Johannf78/Open-Energy-Gateway/src/open_energy_gateway/web_home.h

//Raw string literal quotation, webpage HTML...

String webpage_home = R"(

<!-- Main Content -->
<main class="main-content">
  
  <!-- Header -->
  <header class="header">
    <h1>Home</h1>
  </header>

  <!-- Content -->
  <div class="content">

  <div class="card">
    <p>Connection status: <span id="connection_status" style="color: gray;">Connecting...</span></p>
    <p>Last update: <span id="last_update">--:--:--</span></p>
    <br>
    <p>Values updates every 5 seconds. Initial connection usually takes a few seconds.</p>  
  </div>


  <div class="card">
  <h2>Meter List</h2>
  <p>(Connection typically completes in 2-8 seconds)</p>
    <table>
      <thead>
        <tr>
          <th>Meter</th>
          <th>Serial Number</th>
          <th>Name</th>
          <th>View</th>
        </tr>
      </thead>
      <tbody>
        <tr id="meter-list-row-1">
          <td>1</td>
          <td id="meter_list_m1_serial_number">Loading...</td>
          <td id="meter_list_m1_name" style="text-align: left;">Loading...</td>
          <td><a href="/meters?id=1" class="view-button">View</a></td>
        </tr>
        <tr id="meter-list-row-2">
          <td>2</td>
          <td id="meter_list_m2_serial_number">Loading...</td>
          <td id="meter_list_m2_name" style="text-align: left;">Loading...</td>
          <td><a href="/meters?id=2" class="view-button">View</a></td>
        </tr>
        <tr id="meter-list-row-3">
          <td>3</td>
          <td id="meter_list_m3_serial_number">Loading...</td>
          <td id="meter_list_m3_name" style="text-align: left;">Loading...</td>
          <td><a href="/meters?id=3" class="view-button">View</a></td>
        </tr>
        <tr id="meter-list-row-4">
          <td>4</td>
          <td id="meter_list_m4_serial_number">Loading...</td>
          <td id="meter_list_m4_name" style="text-align: left;">Loading...</td>
          <td><a href="/meters?id=4" class="view-button">View</a></td>
        </tr>
        <tr id="meter-list-row-5">
          <td>5</td>
          <td id="meter_list_m5_serial_number">Loading...</td>
          <td id="meter_list_m5_name" style="text-align: left;">Loading...</td>
          <td><a href="/meters?id=5" class="view-button">View</a></td>
        </tr>
        <tr id="meter-list-row-6">
          <td>6</td>
          <td id="meter_list_m6_serial_number">Loading...</td>
          <td id="meter_list_m6_name" style="text-align: left;">Loading...</td>
          <td><a href="/meters?id=6" class="view-button">View</a></td>
        </tr>
        <tr id="meter-list-row-7">
          <td>7</td>
          <td id="meter_list_m7_serial_number">Loading...</td>
          <td id="meter_list_m7_name" style="text-align: left;">Loading...</td>
          <td><a href="/meters?id=7" class="view-button">View</a></td>
        </tr>
        <tr id="meter-list-row-8">
          <td>8</td>
          <td id="meter_list_m8_serial_number">Loading...</td>
          <td id="meter_list_m8_name" style="text-align: left;">Loading...</td>
          <td><a href="/meters?id=8" class="view-button">View</a></td>
        </tr>
        <tr id="meter-list-row-9">
          <td>9</td>
          <td id="meter_list_m9_serial_number">Loading...</td>
          <td id="meter_list_m9_name" style="text-align: left;">Loading...</td>
          <td><a href="/meters?id=9" class="view-button">View</a></td>
        </tr>
        <tr id="meter-list-row-10">
          <td>10</td>
          <td id="meter_list_m10_serial_number">Loading...</td>
          <td id="meter_list_m10_name" style="text-align: left;">Loading...</td>
          <td><a href="/meters?id=10" class="view-button">View</a></td>
        </tr>
      </tbody>
    </table>
  </div>
  
<div class="card">
  <h2>Energy Consumption Summary (Active energy imported)</h2>
  <table>
  <tr>
    <th>Meter</th>
    <th>L1</th>
    <th>L2</th>
    <th>L3</th>
    <th>Total</th>
  </tr>
  <tr id='m1_active_energy_imported'>
    <td>1</td>
    <td id='m1_active_energy_imported_L1'>0 kWh</td>
    <td id='m1_active_energy_imported_L2'>0 kWh</td>
    <td id='m1_active_energy_imported_L3'>0 kWh</td>
    <td id='m1_active_energy_imported_tot'>0 kWh</td>
  </tr>
  <tr id='m2_active_energy_imported'>
    <td>2</td>
    <td id='m2_active_energy_imported_L1'>0 kWh</td>
    <td id='m2_active_energy_imported_L2'>0 kWh</td>
    <td id='m2_active_energy_imported_L3'>0 kWh</td>
    <td id='m2_active_energy_imported_tot'>0 kWh</td>
  </tr>
  <tr id='m3_active_energy_imported'>
    <td>3</td>
    <td id='m3_active_energy_imported_L1'>0 kWh</td>
    <td id='m3_active_energy_imported_L2'>0 kWh</td>
    <td id='m3_active_energy_imported_L3'>0 kWh</td>
    <td id='m3_active_energy_imported_tot'>0 kWh</td>
  </tr>  
  <tr id='m4_active_energy_imported'>
    <td>4</td>
    <td id='m4_active_energy_imported_L1'>0 kWh</td>
    <td id='m4_active_energy_imported_L2'>0 kWh</td>
    <td id='m4_active_energy_imported_L3'>0 kWh</td>
    <td id='m4_active_energy_imported_tot'>0 kWh</td>
  </tr>
  <tr id='m5_active_energy_imported'>
    <td>5</td>
    <td id='m5_active_energy_imported_L1'>0 kWh</td>
    <td id='m5_active_energy_imported_L2'>0 kWh</td>
    <td id='m5_active_energy_imported_L3'>0 kWh</td>
    <td id='m5_active_energy_imported_tot'>0 kWh</td>
  </tr>
  <tr id='m6_active_energy_imported'>
    <td>6</td>
    <td id='m6_active_energy_imported_L1'>0 kWh</td>
    <td id='m6_active_energy_imported_L2'>0 kWh</td>
    <td id='m6_active_energy_imported_L3'>0 kWh</td>
    <td id='m6_active_energy_imported_tot'>0 kWh</td>
  </tr>
  <tr id='m7_active_energy_imported'>
    <td>7</td>
    <td id='m7_active_energy_imported_L1'>0 kWh</td>
    <td id='m7_active_energy_imported_L2'>0 kWh</td>
    <td id='m7_active_energy_imported_L3'>0 kWh</td>
    <td id='m7_active_energy_imported_tot'>0 kWh</td>
  </tr>
  <tr id='m8_active_energy_imported'>
    <td>8</td>
    <td id='m8_active_energy_imported_L1'>0 kWh</td>
    <td id='m8_active_energy_imported_L2'>0 kWh</td>
    <td id='m8_active_energy_imported_L3'>0 kWh</td>
    <td id='m8_active_energy_imported_tot'>0 kWh</td>
  </tr>
  <tr id='m9_active_energy_imported'>
    <td>9</td>
    <td id='m9_active_energy_imported_L1'>0 kWh</td>
    <td id='m9_active_energy_imported_L2'>0 kWh</td>
    <td id='m9_active_energy_imported_L3'>0 kWh</td>
    <td id='m9_active_energy_imported_tot'>0 kWh</td>
  </tr>
  <tr id='m10_active_energy_imported'>
    <td>10</td>
    <td id='m10_active_energy_imported_L1'>0 kWh</td>
    <td id='m10_active_energy_imported_L2'>0 kWh</td>
    <td id='m10_active_energy_imported_L3'>0 kWh</td>
    <td id='m10_active_energy_imported_tot'>0 kWh</td>
  </tr>
  </table>
  </div>

  <div class="card">
    <h2>Power Consumption Summary (Active power)</h2>
    <table>
    <tr>
      <th>Meter</th>
      <th>L1</th>
      <th>L2</th>
      <th>L3</th>
      <th>Total</th>
    </tr>
    <tr id='m1_active_power'>
      <td>1</td>
      <td id='m1_active_power_L1'>0.00 KW</td>
      <td id='m1_active_power_L2'>0.00 KW</td>
      <td id='m1_active_power_L3'>0.00 KW</td>
      <td id='m1_active_power_tot'>0.00 KW</td>
    </tr>
    <tr id='m2_active_power'>
      <td>2</td>
      <td id='m2_active_power_L1'>0.00 KW</td>
      <td id='m2_active_power_L2'>0.00 KW</td>
      <td id='m2_active_power_L3'>0.00 KW</td>
      <td id='m2_active_power_tot'>0.00 KW</td>
    </tr>    
    <tr id='m3_active_power'>
      <td>3</td>
      <td id='m3_active_power_L1'>0.00 KW</td>
      <td id='m3_active_power_L2'>0.00 KW</td>
      <td id='m3_active_power_L3'>0.00 KW</td>
      <td id='m3_active_power_tot'>0.00 KW</td>
    </tr>
    <tr id='m4_active_power'>
      <td>4</td>
      <td id='m4_active_power_L1'>0.00 KW</td>
      <td id='m4_active_power_L2'>0.00 KW</td>
      <td id='m4_active_power_L3'>0.00 KW</td>
      <td id='m4_active_power_tot'>0.00 KW</td>
    </tr>    
    <tr id='m5_active_power'>
      <td>5</td>
      <td id='m5_active_power_L1'>0.00 KW</td>
      <td id='m5_active_power_L2'>0.00 KW</td>
      <td id='m5_active_power_L3'>0.00 KW</td>
      <td id='m5_active_power_tot'>0.00 KW</td>
    </tr>
    <tr id='m6_active_power'>
      <td>6</td>
      <td id='m6_active_power_L1'>0.00 KW</td>
      <td id='m6_active_power_L2'>0.00 KW</td>
      <td id='m6_active_power_L3'>0.00 KW</td>
      <td id='m6_active_power_tot'>0.00 KW</td>
    </tr>
    <tr id='m7_active_power'>
      <td>7</td>
      <td id='m7_active_power_L1'>0.00 KW</td>
      <td id='m7_active_power_L2'>0.00 KW</td>
      <td id='m7_active_power_L3'>0.00 KW</td>
      <td id='m7_active_power_tot'>0.00 KW</td>
    </tr>
    <tr id='m8_active_power'>
      <td>8</td>
      <td id='m8_active_power_L1'>0.00 KW</td>
      <td id='m8_active_power_L2'>0.00 KW</td>
      <td id='m8_active_power_L3'>0.00 KW</td>
      <td id='m8_active_power_tot'>0.00 KW</td>
    </tr>
    <tr id='m9_active_power'>
      <td>9</td>
      <td id='m9_active_power_L1'>0.00 KW</td>
      <td id='m9_active_power_L2'>0.00 KW</td>
      <td id='m9_active_power_L3'>0.00 KW</td>
      <td id='m9_active_power_tot'>0.00 KW</td>
    </tr>
    <tr id='m10_active_power'>
      <td>10</td>
      <td id='m10_active_power_L1'>0.00 KW</td>
      <td id='m10_active_power_L2'>0.00 KW</td>
      <td id='m10_active_power_L3'>0.00 KW</td>
      <td id='m10_active_power_tot'>0.00 KW</td>
    </tr>
    </table>
  </div>


    </div> <!-- End of content -->
  </main>
</div> <!-- End of app-container -->

<footer>
<br/><br/>
<span><a href='https://ampx.co/' target='_blank'>https://ampx.co</a></span>
</footer>
</body>
<script type="text/javascript">

  // Initialize the socket variable to be used in the connectToWebSocket function
  var socket;
  var reconnectAttempts = 0; // Number of reconnection attempts, this is used to track the number of reconnection attempts.
  var maxReconnectAttempts = 10; // Maximum number of reconnection attempts, this is used to prevent infinite reconnection attempts.
  var maxNumberOfMeters = 10; // Maximum number of meters supported, this is used to limit the number of meters that can be displayed on the web page.

  function init(){
    //This variable is updated by the Arduino code before sending the HTML
    var numberOfMeters = numberOfMetersValue; // Define the number of meters as an integer
  

    // Hide all meter divs and summary rows beyond numberOfMeters
    // Only show the meter divs and summary rows that are needed
    for (let i = 1; i <= maxNumberOfMeters; i++) {
      const energySummaryRow = document.getElementById('m' + i + '_active_energy_imported');
      const powerSummaryRow  = document.getElementById('m' + i + '_active_power');
      const meterListRow = document.getElementById('meter-list-row-' + i);
      
      if (i > numberOfMeters) {
        if (energySummaryRow) energySummaryRow.style.display = 'none';
        if (powerSummaryRow)  powerSummaryRow.style.display  = 'none';
        if (meterListRow) meterListRow.style.display = 'none';
      } else {
        if (energySummaryRow) energySummaryRow.style.display = '';
        if (powerSummaryRow)  powerSummaryRow.style.display  = '';
        if (meterListRow) meterListRow.style.display = '';
      }
    }

    connectToWebSocket();

  }



  function connectToWebSocket(){
  
    socket = new WebSocket('ws://' + window.location.hostname + ':81/');
    
    socket.onopen = function() {
      console.log('WebSocket connected');
      reconnectAttempts = 0; // Reset counter on successful connection
      document.getElementById('connection_status').textContent = 'Connected';
      document.getElementById('connection_status').style.color = 'green';
    };

    socket.onmessage = function(event) {
      //for debugging purposes, log the message to the console
      console.log('WebSocket message received');
      //console.log(event.data);

      processCommand(event);

      //Update the last update time
      var now = new Date();
      document.getElementById('last_update').textContent = now.toLocaleTimeString();
    };

    
    socket.onerror = function(error) {
      console.log('WebSocket error');
    };

    socket.onclose = function(event) {
      console.log('WebSocket closed');

      document.getElementById('connection_status').textContent = 'Disconnected';
      document.getElementById('connection_status').style.color = 'red';

      // Keep trying. Stopping after 10 attempts left the page on Disconnected
      // when the first handshakes landed during a meter read.
      setTimeout(connectToWebSocket, 1000);
    };
  };
  

  function processCommand(event){
    var data = JSON.parse(event.data);
    
    if (data) {
      for (let key in data) {
        let value = data[key];

        //for debugging purposes, log the key and value to the console
        //console.log('Key:', key, 'Value:', value);

        if (key.includes('voltage'))
          value += ' V';
        else if (key.includes('current'))
          value += ' A';
        else if (key.includes('power'))
          value += ' kW';
        else if (key.includes('energy'))
          value += ' kWh';
      else if (key.includes('name'))
          value =  value; // Just use the value directly
      // Note: serial numbers don't need units, so no special handling
           
           
        //console.log("Key:", key, "Value:", value);

        //Use the key to find the element and update the innerHTML
        let element = document.getElementById(key);
        if (element) {
          element.textContent = value;
        }
        
      // Handle meter list table mapping (new functionality)
      if (key.includes('serial_number')) {
        let meterNum = key.match(/m(\d+)_serial_number/)[1];
        let meterListElement = document.getElementById('meter_list_' + key);
        if (meterListElement) {
          meterListElement.textContent = value;
        }
      }
      
      if (key.includes('_name') && !key.includes('summary')) {
        let meterNum = key.match(/m(\d+)_name/)[1];
        let meterListElement = document.getElementById('meter_list_' + key);
        if (meterListElement) {
          meterListElement.textContent = value;
        }
      }

        
      }
    }
  }
  window.onload = function(event){
    init();
  }
</script>
</html>
  )";
