Johannf78/Open-Energy-Gateway/src/open_energy_gateway/functions_web.ino

//Initialise the server and websocket
void initServer() {
  server.on("/", handleRoot);
  server.on("/update", HTTP_POST, handleUpdate);
  server.on("/ota_status", HTTP_GET, handleOtaStatus);
  server.on("/settings", handleSettings);
  server.on("/admin", handleAdmin);
  server.on("/meters", handleMeters);
  server.on("/update_meters_name", HTTP_POST, handleChangeMetersName);
  server.on("/update_gateway_id", HTTP_POST, handleUpdateGatewayId);  // Add this line
  server.on("/reboot_gateway", HTTP_POST, handleRebootGateway); 
  server.on("/clear_wifi", HTTP_POST, handleClearWifi);
  server.begin();
  
  //Handle the websocket events, this is used to handle the connection/disconnection events.
  //function is defined below.
  webSocket.onEvent(webSocketEvent);

  //Initialise the websockets on port 81
  webSocket.begin();
}


// WebSocket event handler - handles connection/disconnection events
void webSocketEvent(uint8_t num, WStype_t type, uint8_t * payload, size_t length) {
  switch(type) {
    case WStype_DISCONNECTED:
      Serial.printf("[%u] Disconnected!\n", num);
      break;
      
    case WStype_CONNECTED:
      {
        IPAddress ip = webSocket.remoteIP(num);
        Serial.printf("[%u] Connected from %d.%d.%d.%d\n", num, ip[0], ip[1], ip[2], ip[3]);
      }
      break;
      
    case WStype_TEXT:
      // Client sent text message (not used in this application)
      Serial.printf("[%u] Received text: %s\n", num, payload);
      break;
      
    case WStype_ERROR:
      Serial.printf("[%u] WebSocket Error!\n", num);
      break;
      
    default:
      // Handle other WebSocket event types
      break;
  }
}

//Handle the root webpage
void handleRoot() {
  //String html = "<h1>AmpX Open Energy Gateway</h1>";
  //String vol = "<h1>Voltage on L1: " + String(voltage_on_L1, 2) + "(V)</h1>";
  //html += vol;
  //the String webpage has been defined in the included file webpage.h

  //Replace the string m1_serial_number with the actual serial number, done here as it does not update regularly like values.
  /*
  webpage_home.replace("m1_serial_number", m1_serial_number);
  webpage_home.replace("m2_serial_number", m2_serial_number);
  web_hwebpage_homeome.replace("m3_serial_number", m3_serial_number);
  webpage_home.replace("m4_serial_number", m4_serial_number);
  */
  
  //the String webpage has been defined in the included file webpage.h
  String webpage_home_local = webpage_home;  // Create local copy to avoid mutating global String
  

  //This must be a server side replacement, as the javascript reacts based on this value.
  webpage_home_local.replace("numberOfMetersValue", String(numberOfMeters));

  //Copy the saved meter names from the preferences to the json doc, this is so that the names can be displayed on the page, even if the names have been changed recently.
  for (int i =1; i <= maxNumberOfMeters ; i++){
    String keyName = "m" + String(i) + "_name";
    //Copy the saved meter name from the preferences to the json doc, this is so that the name can be displayed on the page, even if the name has been changed recently.
    JsonDoc[keyName] = preferences.getString(keyName.c_str());
  }

  //Send the page to the client
  server.send(200, "text/html", web_inc_header + webpage_home_local);
}

//Handle the settings webpage
void handleSettings()
{
  String page = webpage_settings;

  // Only replace numberOfMetersValue (needed for JavaScript)
  page.replace("numberOfMetersValue", String(numberOfMeters));

  // Add static values to JsonDoc for WebSocket transmission
  JsonDoc["m_gateway_id"] = String(GATEWAY_ID);
  JsonDoc["m_connected_meters_num"] = String(numberOfMeters);
  
  // Add meter names to JsonDoc
  /*
  JsonDoc["m1_name"] = preferences.getString("m1_name");
  JsonDoc["m2_name"] = preferences.getString("m2_name");
  JsonDoc["m3_name"] = preferences.getString("m3_name");
  JsonDoc["m4_name"] = preferences.getString("m4_name");
  */
  for (int i = 1; i <= maxNumberOfMeters; i++) {
    String keyName = "m" + String(i) + "_name";
    JsonDoc[keyName] = preferences.getString(keyName.c_str());
  }

  // Add serial numbers to JsonDoc (already done in functions_meter.ino)
  /*
  JsonDoc["m1_serial_number"] = m1_serial_number;
  JsonDoc["m2_serial_number"] = m2_serial_number;
  JsonDoc["m3_serial_number"] = m3_serial_number;
  JsonDoc["m4_serial_number"] = m4_serial_number;
  */
  for (int i = 1; i <= maxNumberOfMeters; i++) {
    String keyName = "m" + String(i) + "_serial_number";
    JsonDoc[keyName] = meterSerialNumbers[i - 1];
  }

  // Add WiFi RSSI to JsonDoc
  int rssi = WiFi.RSSI();
  int percentage = (int)((float)(rssi + 100) * 1.4286);
  if (percentage < 0) percentage = 0;
  else if (percentage > 100) percentage = 100;
  JsonDoc["m_wifi_rssi"] = String(rssi) + "dBm (" + String(percentage) + "%)";

  server.send(200, "text/html",  web_inc_header + page);
}

//Handle the admin webpage
// Do NOT fetch the manifest here (or request a check). Outbound HTTPClient inside a
// WebServer handler hangs the ESP32; HTTPS from loop() on Admin load caused TG1WDT reset.
// Check runs in loop() only after GET /ota_status?refresh.
void handleAdmin()
{
  String page = webpage_admin;
  String available = otaStatusCache.ready ? otaStatusCache.available : "Not checked yet";
  String updateCheck = otaStatusCache.ready ? otaStatusCache.status : "Not checked yet";
  String updateDisabled = "disabled";
  if (otaStatusCache.ready && !otaStatusCache.upToDate) {
    updateDisabled = "";
  }

  page.replace("m_gateway_id", String(GATEWAY_ID));
  page.replace("m_firmware_version", String(FIRMWARE_VERSION));
  page.replace("m_available_version", available);
  page.replace("m_update_check", updateCheck);
  page.replace("m_ota_status", getOtaStatusText());
  page.replace("m_ota_time", getOtaTimeText());
  page.replace("m_manifest_url", String(firmwareManifestURL));
  page.replace("m_update_disabled", updateDisabled);

  server.send(200, "text/html", web_inc_header + page);
}

// Instant JSON from cache (filled by serviceOtaManifestCheck in loop).
void handleOtaStatus() {
  if (server.hasArg("refresh")) {
    requestOtaManifestCheck();
  }

  DynamicJsonDocument doc(384);
  doc["ready"] = otaStatusCache.ready;
  doc["current"] = FIRMWARE_VERSION;
  doc["manifest_url"] = firmwareManifestURL;
  doc["ok"] = otaStatusCache.ok;
  doc["available"] = otaStatusCache.available;
  doc["up_to_date"] = otaStatusCache.upToDate;
  doc["update_available"] = otaStatusCache.updateAvailable;
  doc["status"] = otaStatusCache.status;
  doc["error"] = otaStatusCache.error;

  String json;
  serializeJson(doc, json);
  server.send(200, "application/json", json);
}

// Admin-triggered HTTP OTA: refuse if already latest, else status page then flash.
void handleUpdate() {
  FirmwareManifest manifest;
  if (fetchFirmwareManifest(manifest) && !isNewerVersion(manifest.version, String(FIRMWARE_VERSION))) {
    saveOtaStatus("Already on latest (" + manifest.version + ")");
    String alreadyPage = R"(
      <!DOCTYPE html>
      <html>
      <head>
        <title>Already Up To Date</title>
        <meta name='viewport' content='width=device-width, initial-scale=1'>
        <meta http-equiv="refresh" content="5;url=/admin">
        <style>
          body { background-color: #EEEEEE; font-family: Arial, sans-serif; }
          main { margin: auto; border: 3px solid black; padding: 20px; max-width: 600px; }
        </style>
      </head>
      <body>
        <main>
          <h1>Already on latest</h1>
          <p>This gateway is already running firmware version )" + String(FIRMWARE_VERSION) + R"(.</p>
          <p><a href="/admin">Back to Admin</a></p>
        </main>
      </body>
      </html>
    )";
    server.send(200, "text/html", alreadyPage);
    return;
  }

  String updatingPage = R"(
    <!DOCTYPE html>
    <html>
    <head>
      <title>Firmware Updating</title>
      <meta name='viewport' content='width=device-width, initial-scale=1'>
      <meta http-equiv="refresh" content="60;url=/admin">
      <style>
        body { background-color: #EEEEEE; font-family: Arial, sans-serif; }
        main { margin: auto; border: 3px solid black; padding: 20px; max-width: 600px; }
        .warning { color: orange; font-weight: bold; }
      </style>
    </head>
    <body>
      <main>
        <h1>Updating Firmware...</h1>
        <p class="warning">Downloading and installing firmware.</p>
        <p>Do not power off the gateway. This page will redirect to Admin in about 60 seconds.</p>
        <p>If the page does not redirect, open <a href="/admin">Admin</a> after the device reboots.</p>
      </main>
    </body>
    </html>
  )";

  // Standalone status page (full HTML document — do not prepend site header)
  server.send(200, "text/html", updatingPage);
  server.client().flush();
  delay(500);

  bool ok = doOTAUpdate();
  if (ok) {
    debugln("OTA OK — restarting...");
    delay(300);
    ESP.restart();
  } else {
    debugln("OTA failed or skipped — see Admin last OTA status.");
  }
}

//Handle the meters webpage - shows details for a single meter
void handleMeters() {
  // Get the meter ID from query string
  String meterIdStr = server.arg("id");
  int meterId = meterIdStr.toInt();
  
  // Validate meter ID
  if (meterId < 1 || meterId > maxNumberOfMeters) {
    //default to meter 1 if the meter ID is invalid
    meterId = 1;
  }
  
  
  String html = web_inc_header + webpage_meters;
  
  // Replace METER_NUMBER placeholders with actual meter number
  html.replace("METER_NUMBER", String(meterId));

  // Replace numberOfMetersValue with actual number of connected meters
  html.replace("numberOfMetersValue", String(numberOfMeters));
  
  // Load meter name and serial number to JsonDoc for WebSocket
  String meterPrefix = "m" + String(meterId) + "_";
  String keyName = meterPrefix + "name";
  JsonDoc[keyName] = preferences.getString(keyName.c_str());
  
  String serialKeyName = meterPrefix + "serial_number";
  JsonDoc[serialKeyName] = meterSerialNumbers[meterId - 1];
  
  server.send(200, "text/html", html);
}

void handleWebSocket() {
  String JsonString;

  serializeJson(JsonDoc, JsonString);
  //Send the JSON document to the websocket.
  webSocket.broadcastTXT(JsonString);

  //Serial.println("Sent JSON to websocket");
  //Serial.println(JsonString);
  // Pretty print with indentation of 2 spaces
  //serializeJsonPretty(JsonDoc, Serial);
}

void handleChangeMetersName() {
  /*
  String m1_name = server.arg("m1_name");
  preferences.putString("m1_name", m1_name);
  Serial.println("m1_name: " + m1_name);

  String m2_name = server.arg("m2_name");
  preferences.putString("m2_name", m2_name);
  Serial.println("m2_name: " + m2_name);

  String m3_name = server.arg("m3_name");
  preferences.putString("m3_name", m3_name);
  Serial.println("m3_name: " + m3_name);

  String m4_name = server.arg("m4_name");
  preferences.putString("m4_name", m4_name);
  Serial.println("m4_name: " + m4_name);
  */
  for (int i = 1; i <= numberOfMeters; i++) {
    String keyName = "m" + String(i) + "_name";
    if (server.hasArg(keyName)) {
      String meterName = server.arg(keyName);
      preferences.putString(keyName.c_str(), meterName);
      Serial.println(keyName + ": " + meterName);
    }
  }

  //Send success response
  String successPage = R"(
    <!DOCTYPE html>
    <html>
    <head>
      <title>Meter Names Updated</title>
      <meta name='viewport' content='width=device-width, initial-scale=1'>
      <style>
        body { background-color: #EEEEEE; font-family: Arial, sans-serif; }
        main { margin: auto; border: 3px solid black; padding: 20px; }
        .success { color: green; font-weight: bold; }
      </style>
    </head>
    <body>
      <main>
        <h1>Meter Names Updated Successfully</h1>
        <p class="success">Gateway ID has been updated to: )" + String(GATEWAY_ID) + R"(</p>
        <p><a href="/settings">Back to Settings</a> | <a href="/">Home</a></p>
      </main>
    </body>
    </html>
  )";

  server.send(200, "text/html", web_inc_header + successPage);
}

//Handle the gateway ID update form submission
void handleUpdateGatewayId() {

  // Simple shared password — only AmpX staff should change Gateway ID in the field
  if (!server.hasArg("admin_password") || server.arg("admin_password") != ADMIN_PASSWORD) {
    String denyPage = R"(
      <!DOCTYPE html>
      <html>
      <head>
        <title>Access Denied</title>
        <meta name='viewport' content='width=device-width, initial-scale=1'>
        <style>
          body { background-color: #EEEEEE; font-family: Arial, sans-serif; }
          main { margin: auto; border: 3px solid black; padding: 20px; max-width: 600px; }
          .error { color: red; font-weight: bold; }
        </style>
      </head>
      <body>
        <main>
          <h1>Access Denied</h1>
          <p class="error">Incorrect password. Gateway ID was not changed.</p>
          <p><a href="/admin">Back to Admin</a></p>
        </main>
      </body>
      </html>
    )";
    server.send(403, "text/html", denyPage);
    return;
  }

  if (server.hasArg("gateway_id")) {
    String gatewayIdStr = server.arg("gateway_id");
    int newGatewayId = gatewayIdStr.toInt();
    
    //Validate the input (should be a positive integer)
    if (newGatewayId > 0) {
      saveGatewayId(newGatewayId);
      
      //Send success response
      String successPage = R"(
        <!DOCTYPE html>
        <html>
        <head>
          <title>Gateway ID Updated</title>
          <meta name='viewport' content='width=device-width, initial-scale=1'>
          <style>
            body { background-color: #EEEEEE; font-family: Arial, sans-serif; }
            main { margin: auto; border: 3px solid black; padding: 20px; }
            .success { color: green; font-weight: bold; }
          </style>
        </head>
        <body>
          <main>
            <h1>Gateway ID Updated Successfully</h1>
            <p class="success">Gateway ID has been updated to: )" + String(GATEWAY_ID) + R"(</p>
            <p><a href="/admin">Back to Admin</a> | <a href="/">Home</a></p>
          </main>
        </body>
        </html>
      )";
      server.send(200, "text/html", web_inc_header + successPage);
    } else {
      //Invalid input
      server.send(400, "text/plain", "Invalid Gateway ID. Must be a positive integer.");
    }
  } else {
    //No gateway_id parameter
    server.send(400, "text/plain", "Missing gateway_id parameter");
  }
}

//Handle the gateway reboot form submission
void handleRebootGateway() {
  //Send response page first before rebooting
  String successPage = R"(
    <!DOCTYPE html>
    <html>
    <head>
      <title>Gateway Rebooting</title>
      <meta name='viewport' content='width=device-width, initial-scale=1'>
      <meta http-equiv="refresh" content="30;url=/">
      <style>
        body { background-color: #EEEEEE; font-family: Arial, sans-serif; }
        main { margin: auto; border: 3px solid black; padding: 20px; max-width: 600px; }
        .warning { color: orange; font-weight: bold; }
        .countdown { font-size: 24px; color: #333; }
      </style>
    </head>
    <body>
      <main>
        <h1>Gateway Rebooting...</h1>
        <p class="warning">The gateway is rebooting now.</p>
        <p>This page will automatically redirect to the home page in <span class="countdown">30</span> seconds.</p>
        <p>If the page doesn't redirect automatically, click <a href="/">here</a>.</p>
        <script>
          let countdown = 30;
          const countdownElement = document.querySelector('.countdown');
          const timer = setInterval(() => {
            countdown--;
            if (countdown <= 0) {
              clearInterval(timer);
              countdownElement.textContent = '0';
              window.location.href = '/';
              return;
            }
            countdownElement.textContent = countdown;
          }, 1000);
        </script>
      </main>
    </body>
    </html>
  )";
  
  server.send(200, "text/html", web_inc_header + successPage);
  
  //Delay briefly to ensure the response is sent
  delay(500);

  debugln("Turning off all the LEDs before rebooting...");
  digitalWrite(LED_1_POWER, LOW);
  digitalWrite(LED_2_METER, LOW);
  digitalWrite(LED_3_WIFI, LOW);
  digitalWrite(LED_4_INTERNET, LOW);
  digitalWrite(LED_5_SERVER, LOW);
  delay(300);
  
  //Reboot the ESP32
  debugln("Rebooting gateway...");
  ESP.restart();
}


void handleClearWifi() {
  if (!server.hasArg("admin_password") || server.arg("admin_password") != ADMIN_PASSWORD) {
    String denyPage = R"(
      <!DOCTYPE html>
      <html>
      <head>
        <title>Access Denied</title>
        <meta name='viewport' content='width=device-width, initial-scale=1'>
        <style>
          body { background-color: #EEEEEE; font-family: Arial, sans-serif; }
          main { margin: auto; border: 3px solid black; padding: 20px; max-width: 600px; }
          .error { color: red; font-weight: bold; }
        </style>
      </head>
      <body>
        <main>
          <h1>Access Denied</h1>
          <p class="error">Incorrect password. WiFi was not cleared.</p>
          <p><a href="/admin">Back to Admin</a></p>
        </main>
      </body>
      </html>
    )";
    server.send(403, "text/html", denyPage);
    return;
  }

  String apName = "energy-gateway-" + String(GATEWAY_ID);
  String successPage = R"(
    <!DOCTYPE html>
    <html>
    <head>
      <title>WiFi Cleared</title>
      <meta name='viewport' content='width=device-width, initial-scale=1'>
      <style>
        body { background-color: #EEEEEE; font-family: Arial, sans-serif; }
        main { margin: auto; border: 3px solid black; padding: 20px; max-width: 600px; }
        .warning { color: orange; font-weight: bold; }
      </style>
    </head>
    <body>
      <main>
        <h1>WiFi Cleared - Rebooting</h1>
        <p class="warning">Stored WiFi has been erased. This browser will lose the current network.</p>
        <p>Connect to WiFi access point <strong>)" + apName + R"(</strong> (no password).</p>
        <p>Then open <code>http://192.168.4.1</code> to set the customer WiFi.</p>
      </main>
    </body>
    </html>
  )";

  server.send(200, "text/html", successPage);
  server.client().flush();
  delay(500);

  debugln("Clearing stored WiFi and rebooting into AP mode...");
  clearStoredWifi();

  //Turn off all the LEDs
  digitalWrite(LED_1_POWER, LOW);
  digitalWrite(LED_2_METER, LOW);
  digitalWrite(LED_3_WIFI, LOW);
  digitalWrite(LED_4_INTERNET, LOW);
  digitalWrite(LED_5_SERVER, LOW);
  
  delay(300);
  ESP.restart();
}
