Johannf78/Open-Energy-Gateway/src/open_energy_gateway/web_admin.h

//Raw string literal quotation, webpage HTML...
String webpage_admin = R"(

<!-- Main Content -->
<main class="main-content">

  <header class="header">
    <h1>Admin</h1>
  </header>

  <div class="content">

  <div class="card">
  <h2>Gateway Reboot</h2><br>
  <form action='/reboot_gateway' method='post' onsubmit="return confirm('Reboot the gateway now?');">
    <input type='submit' value='Reboot Gateway'>
  </form>
  </div>

  <div class="card">
  <h2>Firmware Update (OTA)</h2>
  <p>Current firmware version: <strong id="fw_current">m_firmware_version</strong></p>
  <p>Available version: <strong id="fw_available">m_available_version</strong></p>
  <p>Update status: <strong id="fw_status">m_update_check</strong></p>
  <p>Last OTA result: <strong>m_ota_status</strong></p>
  <p>Last OTA time: <strong>m_ota_time</strong></p>
  <p>Manifest: <code>m_manifest_url</code></p>
  <button type="button" id="fw_check_btn">Check for update</button>
  <br><br>
  <form id="fw_update_form" action='/update' method='post' onsubmit="return confirm('Download and install firmware? Device will reboot.');">
    <input id="fw_update_btn" type='submit' value='Update Firmware' m_update_disabled>
  </form>
  </div>

<div class="card">
<h2>Clear WiFi (Ship Mode)</h2>
<p>Erases saved WiFi only. Gateway ID is kept. After reboot, connect to AP <strong>energy-gateway-m_gateway_id</strong> (no password) and open <code>http://192.168.4.1</code>.</p>
<form action='/clear_wifi' method='post' enctype='application/x-www-form-urlencoded' onsubmit="return confirm('Erase stored WiFi and reboot into setup mode?');">
  <label for='clear_wifi_password'>Password: </label>
  <input type='password' id='clear_wifi_password' name='admin_password' autocomplete='off'>
  <br><br>
  <input type='submit' value='Clear WiFi and Reboot'>
</form>
</div>

  <div class="card">
  <h2>Gateway ID Management</h2>
  <form action='/update_gateway_id' method='post' enctype='application/x-www-form-urlencoded'>
    <label for='gateway_id'>Current Gateway ID: </label>
    <span id='current_gateway_id'>m_gateway_id</span>
    <br><br>
    <label for='gateway_id'>Set New Gateway ID: </label>
    <input type='text' id='gateway_id' name='gateway_id' value='m_gateway_id'>
    <br><br>
    <label for='admin_password'>Password: </label>
    <input type='password' id='admin_password' name='admin_password' autocomplete='off'>
    <br><br>
    <input type='submit' value='Update Gateway ID'>
  </form>
  </div>

  
  <p><a href="/">Home</a> | <a href="/settings">Settings</a></p>

  </div>
</main>
</div>
<footer>
<br/><br/>
<span><a href='https://www.ampx.co/' target='_blank'>www.ampx.co</a></span>
</footer>
<script>
  // Cache only on load. Check for update uses /ota_status?refresh; loop() does the HTTPS fetch.
  (function () {
    var availableEl = document.getElementById('fw_available');
    var statusEl = document.getElementById('fw_status');
    var updateBtn = document.getElementById('fw_update_btn');
    var checkBtn = document.getElementById('fw_check_btn');
    var attempts = 0;
    var pollTimer = null;

    function apply(data) {
      if (data.ready) {
        if (availableEl) availableEl.textContent = data.available || 'Unavailable';
        if (statusEl) statusEl.textContent = data.status || 'Unknown';
      }
      if (updateBtn) {
        updateBtn.disabled = !(data.ready && !data.up_to_date);
      }
    }

    function poll() {
      attempts++;
      fetch('/ota_status')
        .then(function (r) { return r.json(); })
        .then(function (data) {
          if (!data.ready && attempts < 20) {
            pollTimer = setTimeout(poll, 1000);
            return;
          }
          if (checkBtn) checkBtn.disabled = false;
          apply(data);
        })
        .catch(function () {
          if (attempts < 10) {
            pollTimer = setTimeout(poll, 1000);
            return;
          }
          if (checkBtn) checkBtn.disabled = false;
          if (availableEl) availableEl.textContent = 'Unavailable';
          if (statusEl) statusEl.textContent = 'Manifest check failed';
        });
    }

    function startCheck() {
      attempts = 0;
      if (pollTimer) {
        clearTimeout(pollTimer);
        pollTimer = null;
      }
      if (checkBtn) checkBtn.disabled = true;
      if (availableEl) availableEl.textContent = 'Checking…';
      if (statusEl) statusEl.textContent = 'Checking…';
      fetch('/ota_status?refresh=1')
        .then(function () { poll(); })
        .catch(function () { poll(); });
    }

    if (checkBtn) checkBtn.addEventListener('click', startCheck);

    // Page load: show cache only. Do not pass refresh (that starts TLS).
    fetch('/ota_status')
      .then(function (r) { return r.json(); })
      .then(apply)
      .catch(function () {});
  })();
</script>
</body>
</html>
  )";
