Johannf78/Open-Energy-Gateway/src/Versions/Version 1.0/open_energy_gateway/functions.ino

void initNvs() {
  if (preferences.begin("app", false)) {
    Serial.println("NVS initialized successfully!");
  } else {
    Serial.println("Failed to initialize NVS.");
  }
  Serial.println("");
}

//Add new function prototypes here...
//For all functions that there is not specific category for, add them here.
